CPSdrone/CPS/programs/6.1 proffessional with IMU & PID/more_orientation_display/more_orientation_display.ino

#include <Wire.h>
#include <Kalman.h> // Source: https://github.com/TKJElectronics/KalmanFilter
#include <Adafruit_LSM9DS1.h>
#include <Adafruit_Sensor.h>  // not used in this demo but required!

// i2c
Adafruit_LSM9DS1 lsm = Adafruit_LSM9DS1();

#define LSM9DS1_SCK A5
#define LSM9DS1_MISO 12
#define LSM9DS1_MOSI A4
#define LSM9DS1_XGCS 6
#define LSM9DS1_MCS 5

//#define RESTRICT_PITCH // Comment out to restrict roll to ±90deg instead - please read: http://www.freescale.com/files/sensors/doc/app_note/AN3461.pdf

Kalman kalmanX, kalmanY, kalmanZ; // Create the Kalman instances

/* IMU Data */
double accX, accY, accZ;
double gyroX, gyroY, gyroZ;
double magX, magY, magZ;
int16_t tempRaw;

double roll, pitch, yaw; // Roll and pitch are calculated using the accelerometer while yaw is calculated using the magnetometer

double gyroXangle, gyroYangle, gyroZangle; // Angle calculate using the gyro only
double compAngleX, compAngleY, compAngleZ; // Calculated angle using a complementary filter
double kalAngleX, kalAngleY, kalAngleZ; // Calculated angle using a Kalman filter

uint32_t timer;

void setupSensor()
{
  // 1.) Set the accelerometer range
  lsm.setupAccel(lsm.LSM9DS1_ACCELRANGE_2G);
  //lsm.setupAccel(lsm.LSM9DS1_ACCELRANGE_4G);
  //lsm.setupAccel(lsm.LSM9DS1_ACCELRANGE_8G);
  //lsm.setupAccel(lsm.LSM9DS1_ACCELRANGE_16G);
  
  // 2.) Set the magnetometer sensitivity
  lsm.setupMag(lsm.LSM9DS1_MAGGAIN_4GAUSS);
  //lsm.setupMag(lsm.LSM9DS1_MAGGAIN_8GAUSS);
  //lsm.setupMag(lsm.LSM9DS1_MAGGAIN_12GAUSS);
  //lsm.setupMag(lsm.LSM9DS1_MAGGAIN_16GAUSS);

  // 3.) Setup the gyroscope
  lsm.setupGyro(lsm.LSM9DS1_GYROSCALE_245DPS);
  //lsm.setupGyro(lsm.LSM9DS1_GYROSCALE_500DPS);
  //lsm.setupGyro(lsm.LSM9DS1_GYROSCALE_2000DPS);
}


void setup() {
  Serial.begin(115200);

  while (!Serial) {
    delay(1); // will pause Zero, Leonardo, etc until serial console opens
  }
  
  Serial.println("LSM9DS1 data read demo");
  
  // Try to initialise and warn if we couldn't detect the chip
  if (!lsm.begin())
  {
    Serial.println("Oops ... unable to initialize the LSM9DS1. Check your wiring!");
    while (1);
  }
  Serial.println("Found LSM9DS1 9DOF");

  
  //Wire.begin(); //maybe needed, prob not cuz its for i2c
  setupSensor();
  lsm.read();  /* ask it to read in the data */ 
  /* Get a new sensor event */ 

  
  /* Set Kalman and gyro starting angle */
  updatesensors(); //get accel, gyro, mag, temp vals and name
  updatePitchRoll();
  updateYaw();

  kalmanX.setAngle(roll); // First set roll starting angle
  gyroXangle = roll;
  compAngleX = roll;

  kalmanY.setAngle(pitch); // Then pitch
  gyroYangle = pitch;
  compAngleY = pitch;

  kalmanZ.setAngle(yaw); // And finally yaw
  gyroZangle = yaw;
  compAngleZ = yaw;

  timer = micros(); // Initialize the timer
}

void loop() {
  /* Update all the IMU values */
  lsm.read();  /* ask it to read in the data */ 
  /* Get a new sensor event */ 

  
  updatesensors();

  double dt = (double)(micros() - timer) / 1000000; // Calculate delta time
  timer = micros();


  /* Roll and pitch estimation */
  updatePitchRoll();
  //double gyroXrate = gyroX / 131.0; // Convert to deg/s //prob not needed
  //double gyroYrate = gyroY / 131.0; // Convert to deg/s

#ifdef RESTRICT_PITCH
  // This fixes the transition problem when the accelerometer angle jumps between -180 and 180 degrees
  if ((roll < -90 && kalAngleX > 90) || (roll > 90 && kalAngleX < -90)) {
    kalmanX.setAngle(roll);
    compAngleX = roll;
    kalAngleX = roll;
    gyroXangle = roll;
  } else
    kalAngleX = kalmanX.getAngle(roll, gyroX, dt); // Calculate the angle using a Kalman filter

  if (abs(kalAngleX) > 90)
    gyroY = -gyroY; // Invert rate, so it fits the restricted accelerometer reading
  kalAngleY = kalmanY.getAngle(pitch, gyroY, dt);
#else
  // This fixes the transition problem when the accelerometer angle jumps between -180 and 180 degrees
  if ((pitch < -90 && kalAngleY > 90) || (pitch > 90 && kalAngleY < -90)) {
    kalmanY.setAngle(pitch);
    compAngleY = pitch;
    kalAngleY = pitch;
    gyroYangle = pitch;
  } else
    kalAngleY = kalmanY.getAngle(pitch, gyroY, dt); // Calculate the angle using a Kalman filter

  if (abs(kalAngleY) > 90)
    gyroX = -gyroX; // Invert rate, so it fits the restricted accelerometer reading
  kalAngleX = kalmanX.getAngle(roll, gyroX, dt); // Calculate the angle using a Kalman filter
#endif


  /* Yaw estimation */
  updateYaw();
  //double gyroZrate = gyroZ / 131.0; // Convert to deg/s  //prob not needed
  // This fixes the transition problem when the yaw angle jumps between -180 and 180 degrees
  if ((yaw < -90 && kalAngleZ > 90) || (yaw > 90 && kalAngleZ < -90)) {
    kalmanZ.setAngle(yaw);
    compAngleZ = yaw;
    kalAngleZ = yaw;
    gyroZangle = yaw;
  } else
    kalAngleZ = kalmanZ.getAngle(yaw, gyroZ, dt); // Calculate the angle using a Kalman filter


  /* Estimate angles using gyro only */
  //gyroXangle += gyroX * dt; // Calculate gyro angle without any filter
  //gyroYangle += gyroY * dt;
  //gyroZangle += gyroZ * dt;
  gyroXangle += kalmanX.getRate() * dt; // Calculate gyro angle using the unbiased rate from the Kalman filter
  gyroYangle += kalmanY.getRate() * dt;
  gyroZangle += kalmanZ.getRate() * dt;

  /* Estimate angles using complimentary filter */
  compAngleX = 0.7 * (compAngleX + gyroX * dt) + 0.3 * roll; // Calculate the angle using a Complimentary filter
  compAngleY = 0.7 * (compAngleY + gyroY * dt) + 0.3 * pitch; //originally 0.93, 0.07 everywhere
  compAngleZ = 0.7 * (compAngleZ + gyroZ * dt) + 0.3 * yaw;

  // Reset the gyro angles when they has drifted too much
  if (gyroXangle < -180 || gyroXangle > 180)
    gyroXangle = kalAngleX;
  if (gyroYangle < -180 || gyroYangle > 180)
    gyroYangle = kalAngleY;
  if (gyroZangle < -180 || gyroZangle > 180)
    gyroZangle = kalAngleZ;


  /* Print Data */
#if 1
  Serial.print(roll); Serial.print("\t");
  Serial.print(gyroXangle); Serial.print("\t");
  Serial.print(compAngleX); Serial.print("\t");
  Serial.print(kalAngleX); Serial.print("\t");

  Serial.print("\t");

  Serial.print(pitch); Serial.print("\t");
  Serial.print(gyroYangle); Serial.print("\t");
  Serial.print(compAngleY); Serial.print("\t");
  Serial.print(kalAngleY); Serial.print("\t");

  Serial.print("\t");

  Serial.print(yaw); Serial.print("\t");
  Serial.print(gyroZangle); Serial.print("\t");
  Serial.print(compAngleZ); Serial.print("\t");
  Serial.print(kalAngleZ); Serial.println("\t");

  
#endif
#if 0 // Set to 1 to print the IMU data
  Serial.print("Accel X: "); Serial.print(a.acceleration.x); Serial.print(" m/s^2");
  Serial.print("\tY: "); Serial.print(a.acceleration.y);     Serial.print(" m/s^2 ");
  Serial.print("\tZ: "); Serial.print(a.acceleration.z);     Serial.println(" m/s^2 ");

  Serial.print("Mag X: "); Serial.print(m.magnetic.x);   Serial.print(" gauss");
  Serial.print("\tY: "); Serial.print(m.magnetic.y);     Serial.print(" gauss");
  Serial.print("\tZ: "); Serial.print(m.magnetic.z);     Serial.println(" gauss");

  Serial.print("Gyro X: "); Serial.print(g.gyro.x);   Serial.print(" dps");
  Serial.print("\tY: "); Serial.print(g.gyro.y);      Serial.print(" dps");
  Serial.print("\tZ: "); Serial.print(g.gyro.z);      Serial.println(" dps");

  Serial.print("Temp: "); Serial.print(temp.temperature); Serial.println(" celcius");
#endif
#if 0 // Set to 1 to print the temperature
  Serial.print("\t");
  sensors_event_t a, m, g, temp;
  lsm.getEvent(&a, &m, &g, &temp); 
  double temperature = temp.temperature / 340.0 + 36.53;
  Serial.print("Temp: "); Serial.print(temperature); Serial.println(" celcius");
#endif

  Serial.println();

  delay(00);
}

void updatesensors() {
   // Get accelerometer and gyroscope values, maybe manual get vals once again here? <--
    sensors_event_t a, m, g, temp;
    lsm.getEvent(&a, &m, &g, &temp);
  accX = a.acceleration.x;
  accY = a.acceleration.y;
  accZ = a.acceleration.z;
  //tempRaw = ?? , also i think its prepared, not raw
  gyroX = g.gyro.x;
  gyroY = g.gyro.y;
  gyroZ = g.gyro.z;
  magX = m.magnetic.x;
  magZ = m.magnetic.y;
  magY = m.magnetic.z;
}

void updatePitchRoll() {
  // Source: http://www.freescale.com/files/sensors/doc/app_note/AN3461.pdf eq. 25 and eq. 26
  // atan2 outputs the value of -π to π (radians) - see http://en.wikipedia.org/wiki/Atan2
  // It is then converted from radians to degrees
#ifdef RESTRICT_PITCH // Eq. 25 and 26
  roll = atan2(accY, accZ) * RAD_TO_DEG;
  pitch = atan(-accX / sqrt(accY * accY + accZ * accZ)) * RAD_TO_DEG;
#else // Eq. 28 and 29
  roll = atan(accY / sqrt(accX * accX + accZ * accZ)) * RAD_TO_DEG;
  pitch = atan2(-accX, accZ) * RAD_TO_DEG;
#endif
}

void updateYaw() { // See: http://www.freescale.com/files/sensors/doc/app_note/AN4248.pdf
  magX *= -1; // Invert axis - prob not needed
  magZ *= -1;

  /*double mag_norm = sqrt((magX*magX)+(magY*magY)+(magZ*magZ));
  magX=magX/mag_norm;
  magY=magY/mag_norm;
  magZ=magZ/mag_norm;*/

  double rollAngle = compAngleX * DEG_TO_RAD;  //originally kalAngle
  double pitchAngle = compAngleY * DEG_TO_RAD;

  double Bfy = magZ * sin(rollAngle) - magY * cos(rollAngle);
  double Bfx = magX * cos(pitchAngle) + magY * sin(pitchAngle) * sin(rollAngle) + magZ * sin(pitchAngle) * cos(rollAngle);
  yaw = atan2(-Bfy, Bfx) * RAD_TO_DEG;

  //yaw = atan(accZ / sqrt(accX*accX + accZ*accZ)) * RAD_TO_DEG;
  //yaw = atan2(accX, accY) * RAD_TO_DEG;
  
  yaw *= -1; //prob not needed
}
