CPSdrone/CPS/programs/5.0 OSD & everything for Explory finals/first_OSD_and_cleanup/module_osd.ino

//if(voltup>3.3)&&(voltup<3.5){
// unsigned long t = micros()/10;
// if(t<15){
//  osd.print("Module detected", 13, 7);
//  osd.print("ROBOT ARM on the top", 12, 8);
// }else{
//  for(int d = 13; d<=20; d++) osd.printMax7456Char(0x00,d,7);
//  for(int e = 12; e<=25; e++) osd.printMax7456Char(0x00,e,8);
//  }
// osd.print("arm", 21, 13);
// osd.print(conLAP, 25, 13, 3, 0, false, true);
//}else{
// for(int f = 21; f <= 27; f++){
// osd.printMax7456Char(0x00,f,13);
//}
//}
//
//if(voltup>4.45)&&(voltup<4.65){
// unsigned long t = micros()/10;
// if(t<15){
//  osd.print("Module detected", 13, 7);
//  osd.print("PROBE on the top", 12, 8);
// }else{
//  for(int d = 13; d<=20; d++) osd.printMax7456Char(0x00,d,7);
//  for(int e = 12; e<=25; e++) osd.printMax7456Char(0x00,e,8);
//  }
// osd.print("pro", 21, 11);
// osd.print(conPRO, 25, 11, 3, 0, false, true);
//}else{
// for(int f = 21; f <= 27; f++){
// osd.printMax7456Char(0x00,f,11);
//}
//}
//
//if(voltup>2.4)&&(voltup<2.6){
// unsigned long t = micros()/10;
// if(t<15){
//  osd.print("Module detected", 13, 7);
//  osd.print("pH meter on the top", 12, 8);
// }else{
//  for(int d = 13; d<=20; d++) osd.printMax7456Char(0x00,d,7);
//  for(int e = 12; e<=25; e++) osd.printMax7456Char(0x00,e,8);
//  }
// osd.print("pro", 21, 11);
// osd.print(conPRO, 25, 11, 3, 0, false, true);
//}else{
// for(int f = 21; f <= 27; f++){
// osd.printMax7456Char(0x00,f,11);
//}
//}
//
//if(voltright>2.4)&&(voltup<2.6){
// unsigned long t = micros()/10;
// if(t<15){
//  osd.print("Module detected", 13, 7);
//  osd.print("pH meter on the top", 12, 8);
// }else{
//  for(int d = 13; d<=20; d++) osd.printMax7456Char(0x00,d,7);
//  for(int e = 12; e<=25; e++) osd.printMax7456Char(0x00,e,8);
//  }
// osd.print("pro", 21, 11);
// osd.print(conPRO, 25, 11, 3, 0, false, true);
//}else{
// for(int f = 21; f <= 27; f++){
// osd.printMax7456Char(0x00,f,11);
//}
//}
